Annie-Zhu1210/CASA0021_GPP_Group1/Media/Images/WelcomePage2.jpg

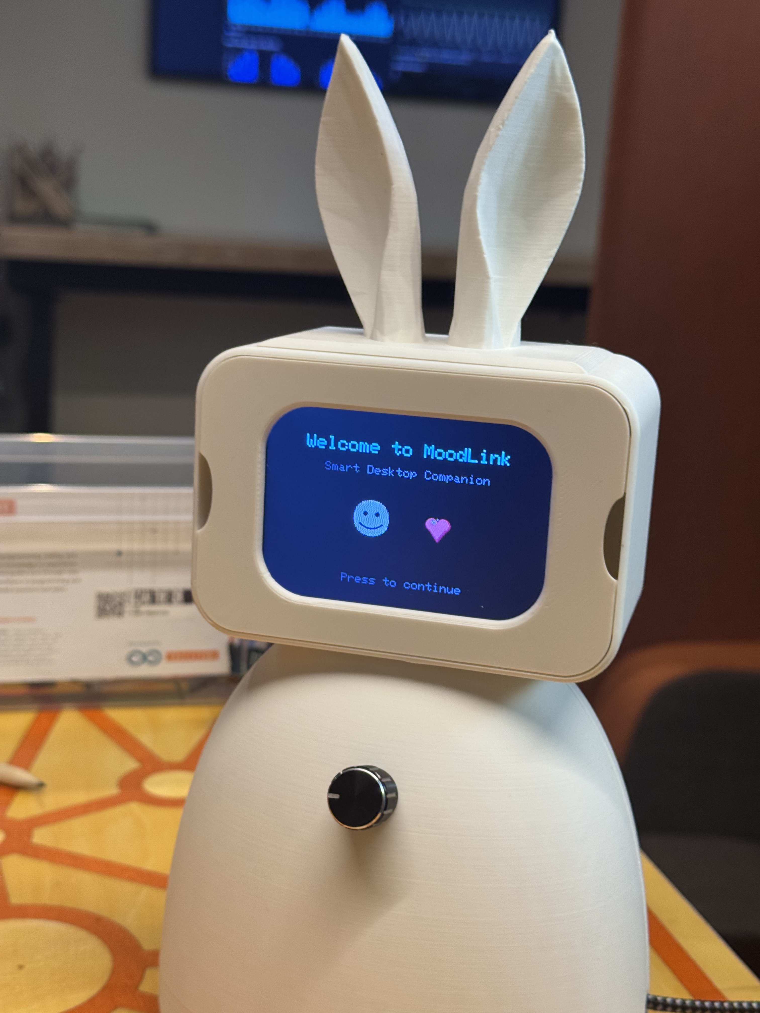
Media/Images/WelcomePage2.jpg
